AirMQ/AirMQ-sensor/Hardware/Case for 3D print/M4 Knob.jpg

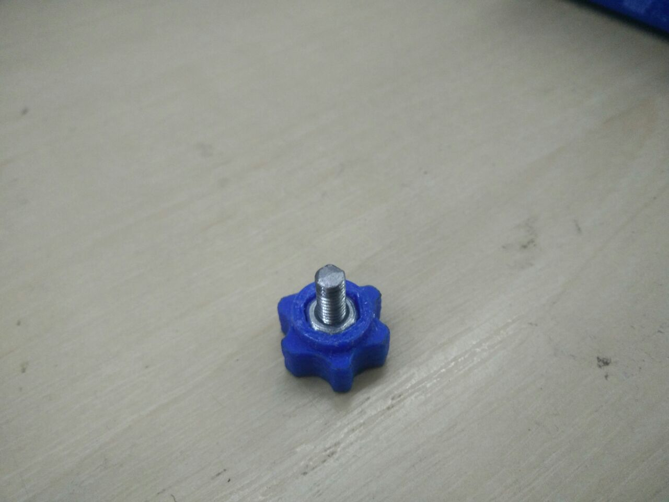
Hardware/Case for 3D print/M4 Knob.jpg
